tioluigidev/Tio-Luigis-IOT-Minilab/images/pictures/minilab-003.jpg

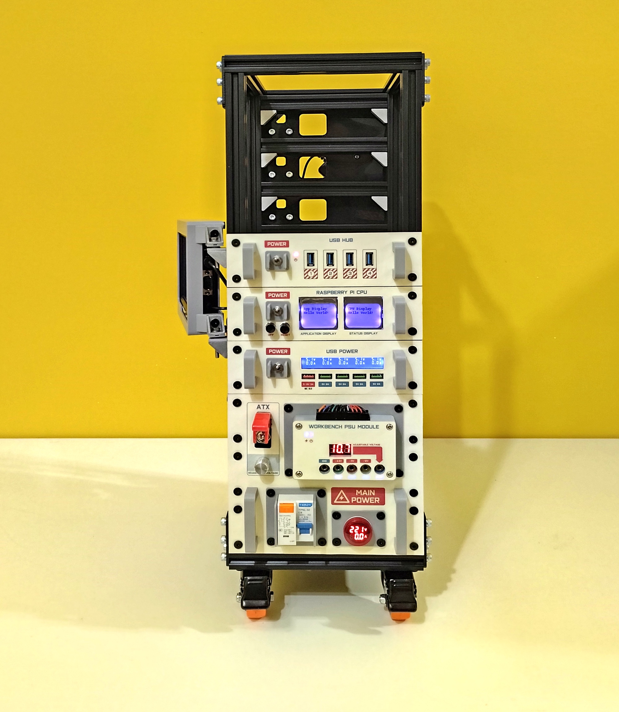
images/pictures/minilab-003.jpg
