tioluigidev/Tio-Luigis-IOT-Minilab/3dprint/module-psu/psu.panel.modulecover2.stl

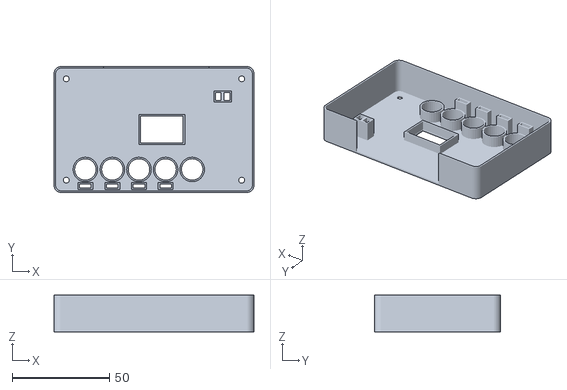
[picture p88: CAD file, 2023-10-16]
3dprint/module-psu/psu.panel.modulecover2.stl
102.6 x 64.6 x 18.8
