tioluigidev/Tio-Luigis-IOT-Minilab/3dprint/module-usbhub/usbhub.innersupport.right.stl

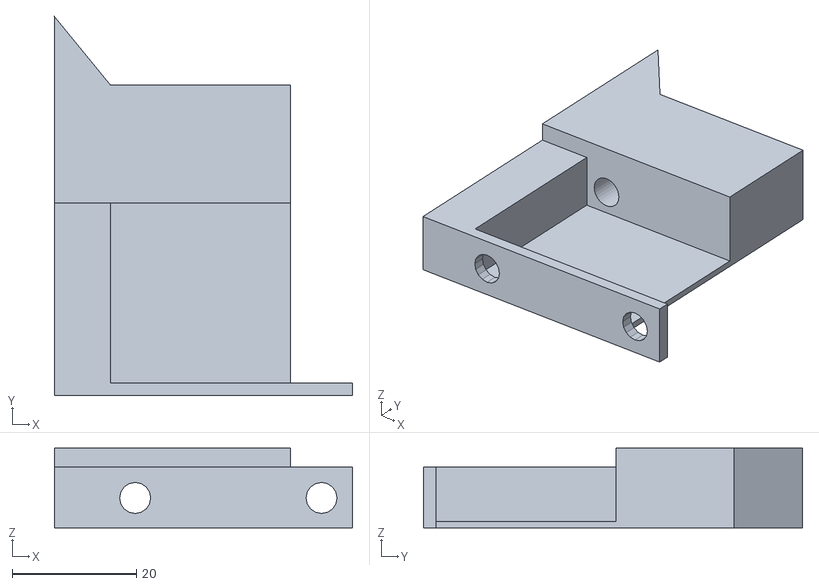
[picture p89: CAD file, 2023-10-16]
3dprint/module-usbhub/usbhub.innersupport.right.stl
48.0 x 61.0 x 12.8
