tioluigidev/Tio-Luigis-IOT-Minilab/3dprint/module-usbpower/usbpower.panel.front.stl

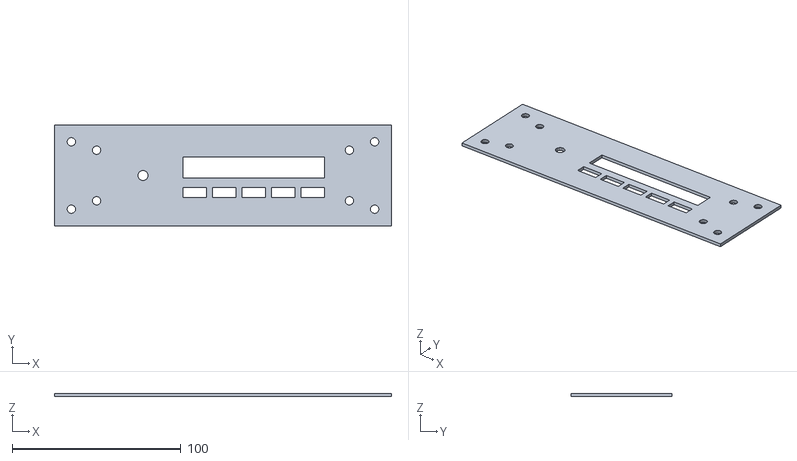
[picture p90: CAD file, 2023-10-16]
3dprint/module-usbpower/usbpower.panel.front.stl
200.0 x 60.0 x 2.00
