tioluigidev/Tio-Luigis-IOT-Minilab/3dprint/rear/rear.cableguide.model2.stl

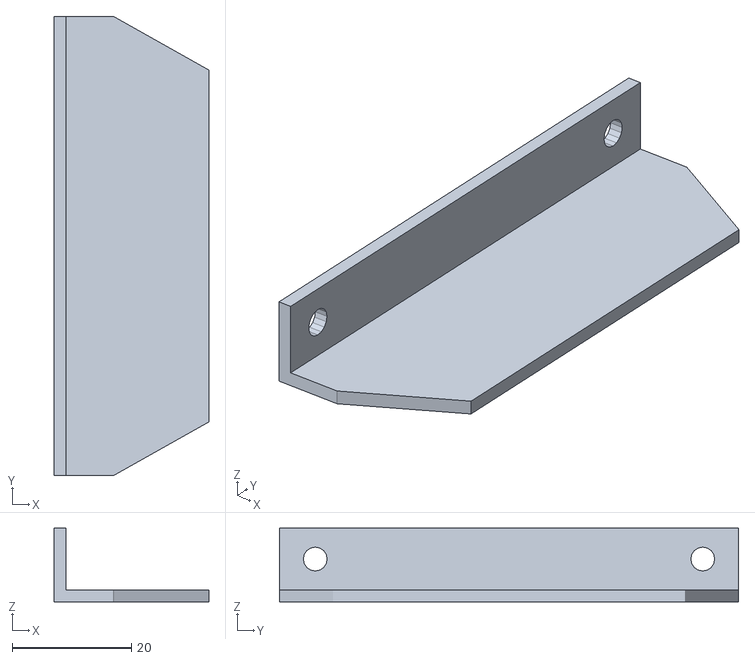
[picture p91: CAD file, 2023-10-15]
3dprint/rear/rear.cableguide.model2.stl
26.0 x 77.0 x 12.4
