tioluigidev/Tio-Luigis-IOT-Minilab/3dprint/module-psu/psu.panel.potentiometersupport.stl

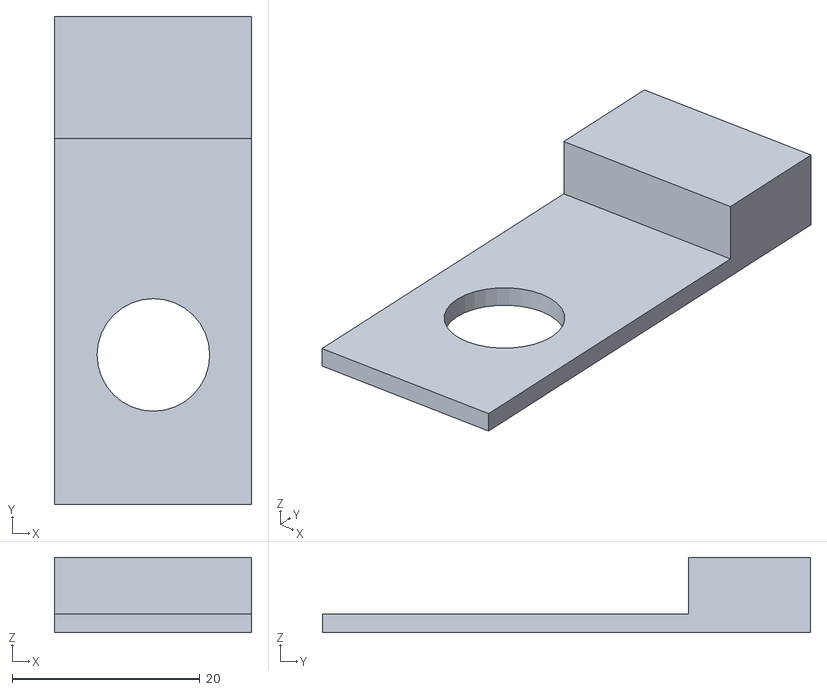
[picture p92: CAD file, 2023-10-16]
3dprint/module-psu/psu.panel.potentiometersupport.stl
21.0 x 52.0 x 8.00
