tioluigidev/Tio-Luigis-IOT-Minilab/3dprint/module-usbpower/usbpower.innersupport.left.stl

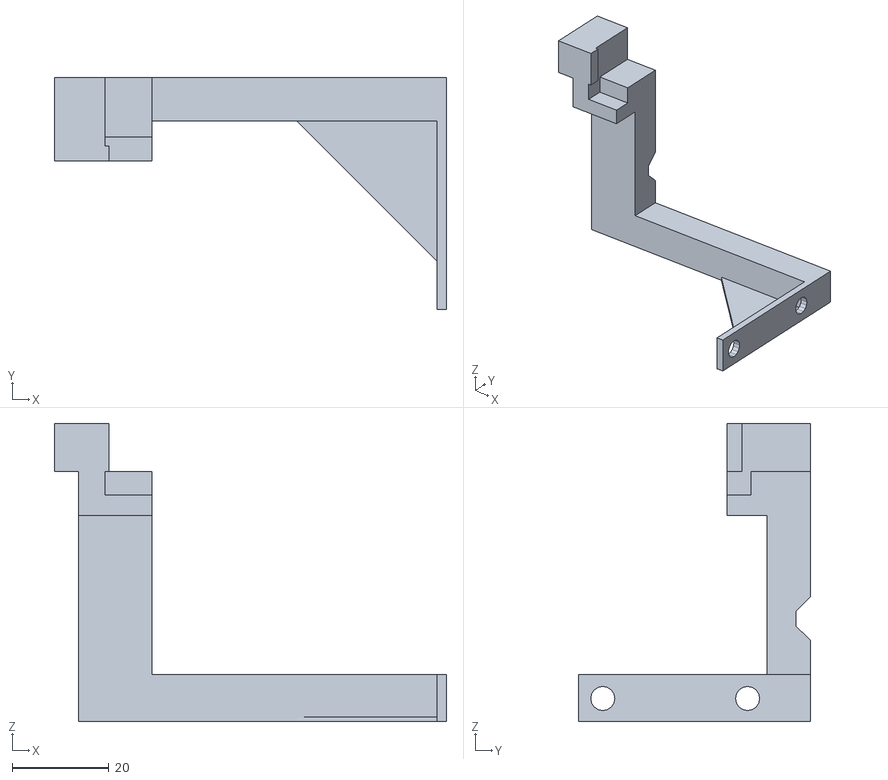
[picture p93: CAD file, 2023-10-16]
3dprint/module-usbpower/usbpower.innersupport.left.stl
81.2 x 48.0 x 61.8
