tioluigidev/Tio-Luigis-IOT-Minilab/3dprint/rear/rear.cableguide.model1.stl

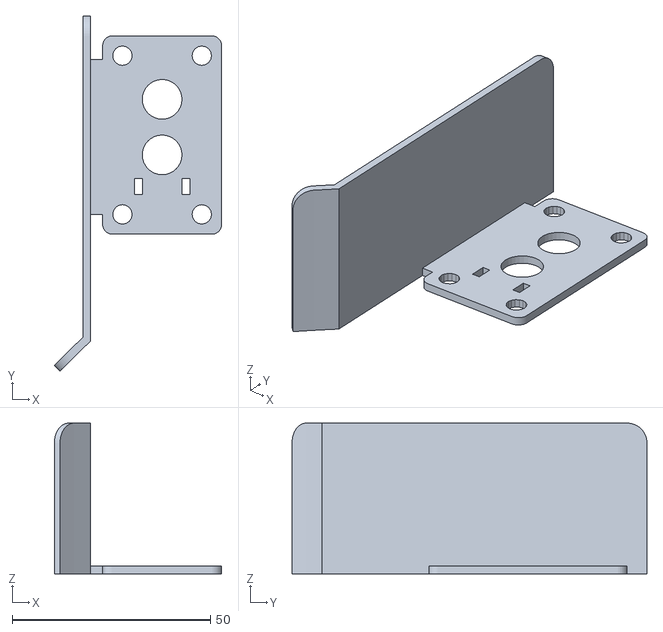
[picture p94: CAD file, 2023-10-15]
3dprint/rear/rear.cableguide.model1.stl
42.1 x 89.5 x 38.0
