tioluigidev/Tio-Luigis-IOT-Minilab/3dprint/module-psu/psu.cableguide.stl

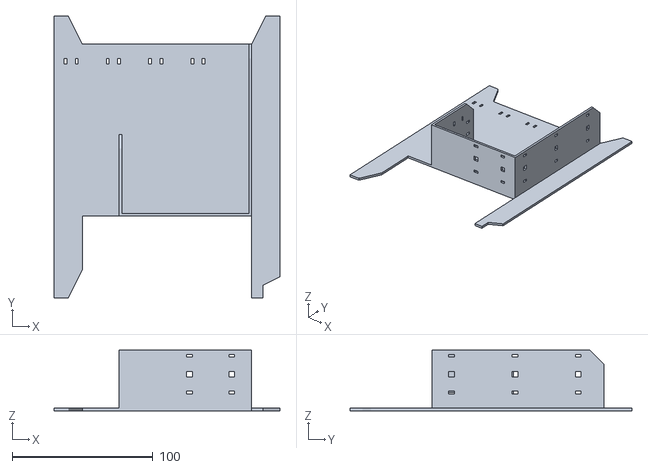
[picture p95: CAD file, 2023-10-16]
3dprint/module-psu/psu.cableguide.stl
160.0 x 200.0 x 43.0
