tioluigidev/Tio-Luigis-IOT-Minilab/3dprint/module-rpicpu/rpicpu.panel.front.stl

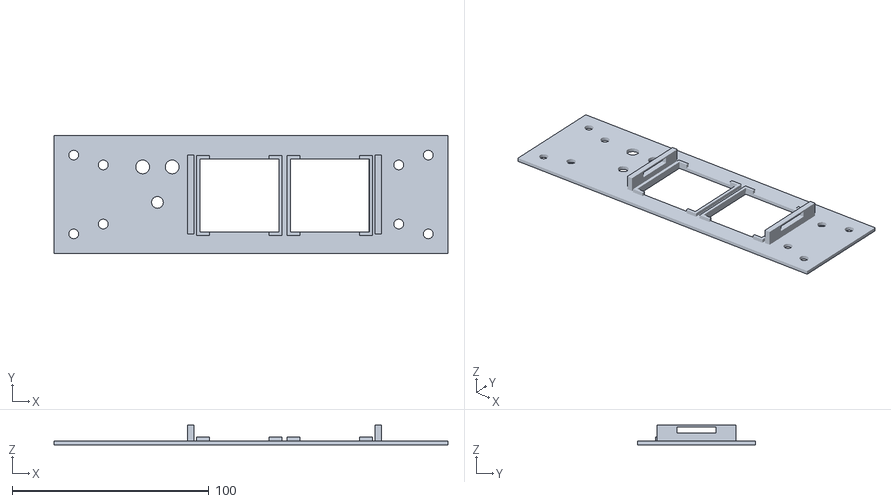
[picture p96: CAD file, 2023-11-06]
3dprint/module-rpicpu/rpicpu.panel.front.stl
200.0 x 60.0 x 10.0
