tioluigidev/Tio-Luigis-IOT-Minilab/3dprint/module-usbhub/usbhub.innersupport.middle.stl

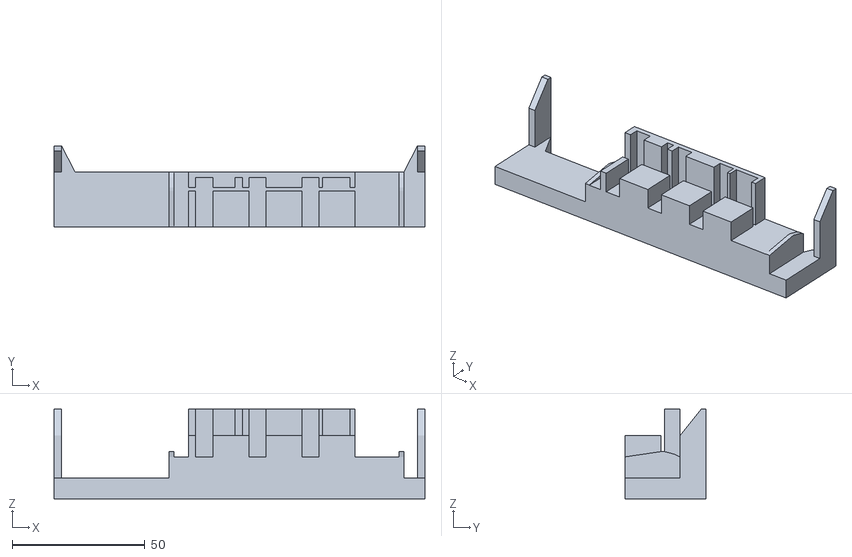
[picture p97: CAD file, 2023-10-16]
3dprint/module-usbhub/usbhub.innersupport.middle.stl
139.8 x 30.7 x 33.8
