tioluigidev/Tio-Luigis-IOT-Minilab/3dprint/module-usbpower/usbpower.panel.handler.stl

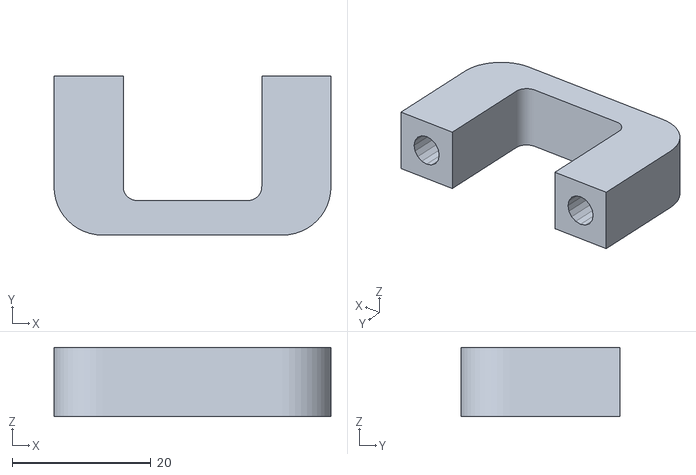
[picture p98: CAD file, 2023-10-16]
3dprint/module-usbpower/usbpower.panel.handler.stl
40.0 x 23.0 x 10.0
