tioluigidev/Tio-Luigis-IOT-Minilab/3dprint/rear/rear.baycover.psu.stl

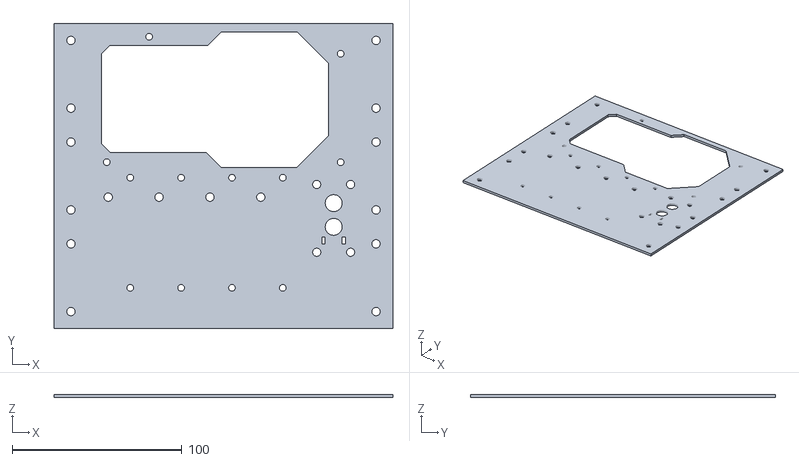
[picture p99: CAD file, 2023-10-15]
3dprint/rear/rear.baycover.psu.stl
200.0 x 180.0 x 2.00
