tioluigidev/Tio-Luigis-IOT-Minilab/3dprint/module-psu/psu.circuitbreakersupport.stl

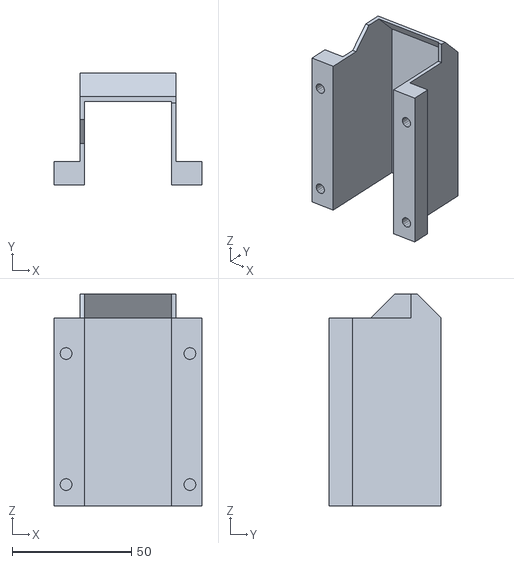
[picture p100: CAD file, 2023-10-16]
3dprint/module-psu/psu.circuitbreakersupport.stl
62.0 x 47.2 x 89.0
