tioluigidev/Tio-Luigis-IOT-Minilab/3dprint/module-rpicpu/rpicpu.base.stl

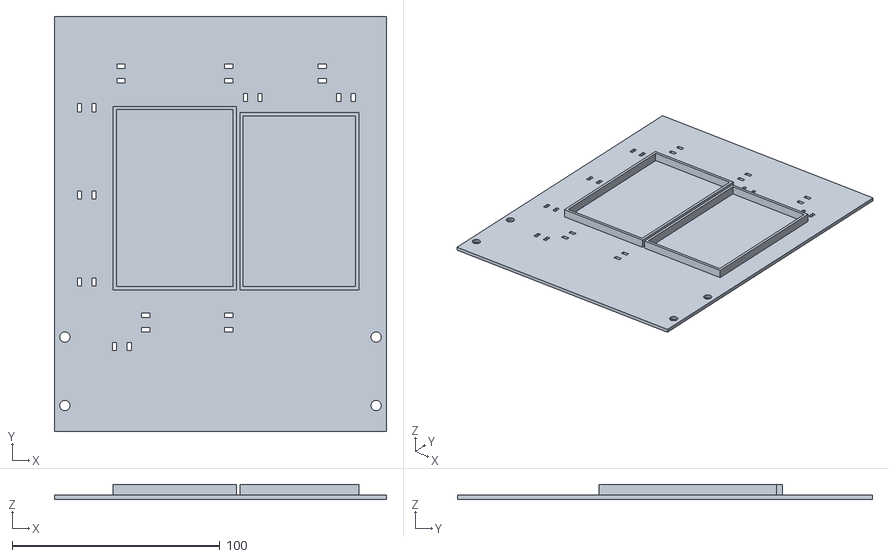
[picture p101: CAD file, 2023-11-06]
3dprint/module-rpicpu/rpicpu.base.stl
160.0 x 200.0 x 7.00
