tioluigidev/Tio-Luigis-IOT-Minilab/3dprint/module-usbpower/usbpower.innersupport.right.stl

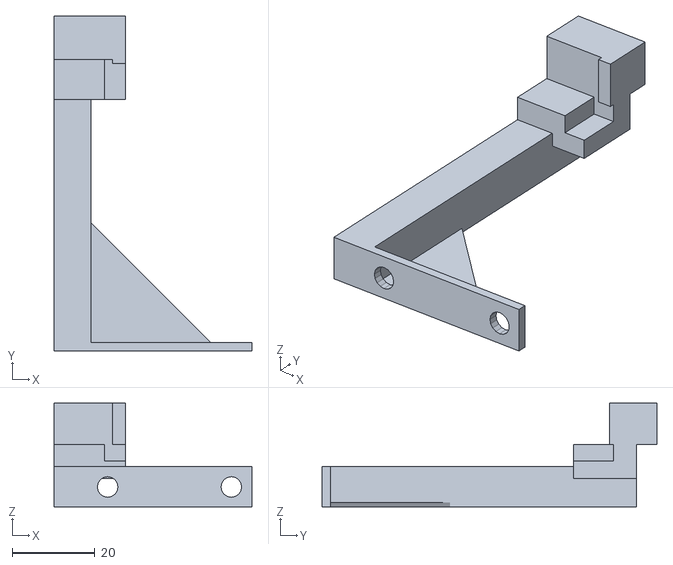
[picture p102: CAD file, 2023-10-16]
3dprint/module-usbpower/usbpower.innersupport.right.stl
48.0 x 81.2 x 25.1
