tioluigidev/Tio-Luigis-IOT-Minilab/3dprint/rear/rear.cableguide.model4.stl

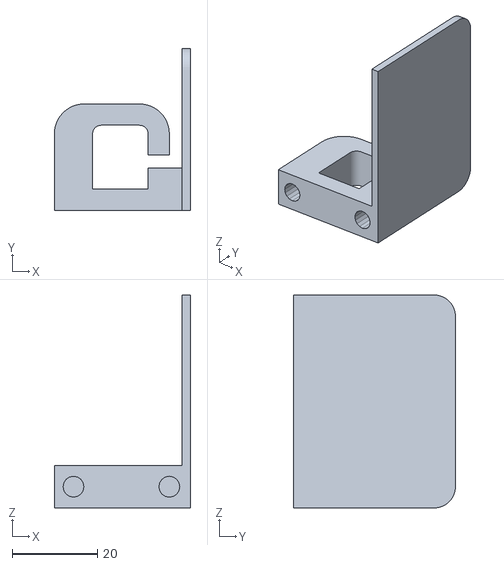
[picture p103: CAD file, 2023-10-15]
3dprint/rear/rear.cableguide.model4.stl
32.0 x 38.0 x 50.0
