tioluigidev/Tio-Luigis-IOT-Minilab/3dprint/module-psu/psu.panel.front.stl

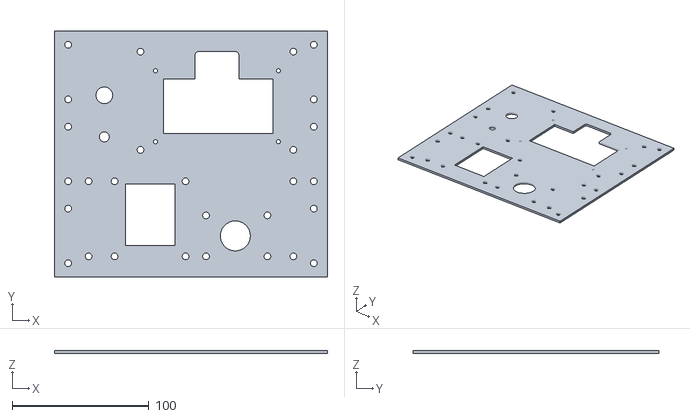
[picture p104: CAD file, 2023-10-16]
3dprint/module-psu/psu.panel.front.stl
200.0 x 180.0 x 2.00
