tioluigidev/Tio-Luigis-IOT-Minilab/3dprint/rear/rear.cableguide.model3.stl

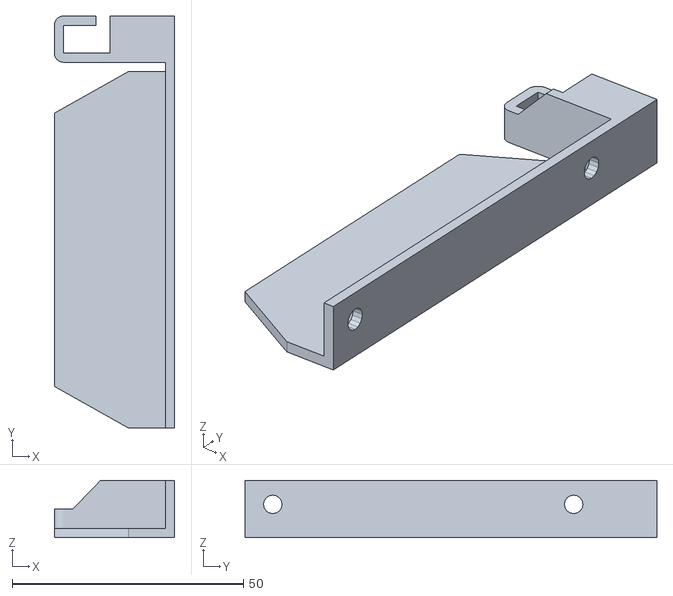
[picture p105: CAD file, 2023-10-15]
3dprint/rear/rear.cableguide.model3.stl
26.0 x 89.0 x 12.4
