tioluigidev/Tio-Luigis-IOT-Minilab/3dprint/module-psu/psu.panel.handler.stl

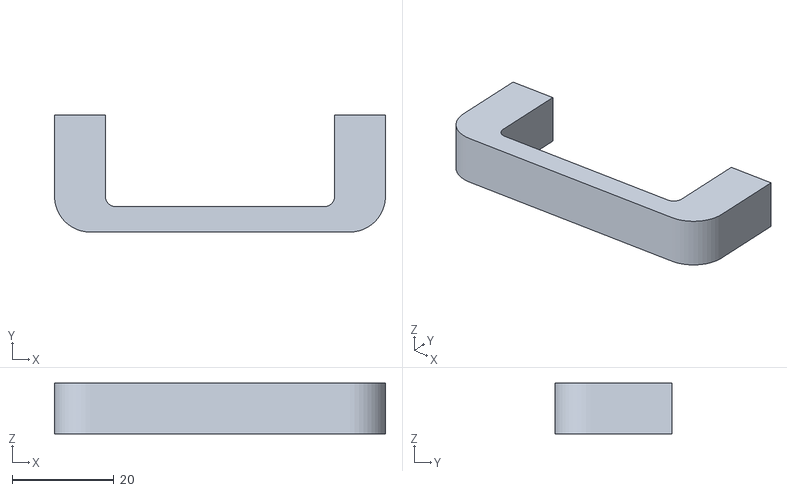
[picture p106: CAD file, 2023-10-16]
3dprint/module-psu/psu.panel.handler.stl
65.0 x 23.0 x 10.0
