tioluigidev/Tio-Luigis-IOT-Minilab/3dprint/module-psu/psu.panel.modulecover1.stl

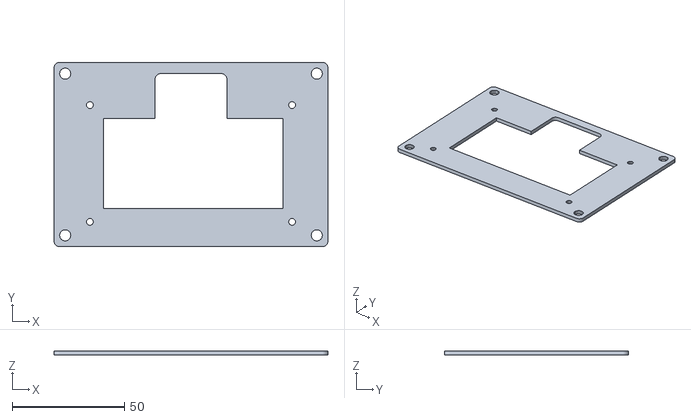
[picture p107: CAD file, 2023-10-16]
3dprint/module-psu/psu.panel.modulecover1.stl
122.0 x 82.0 x 2.00
